siorTeam/smart-pen/week5/Nano_33ble/Python-Data-Sampling-App/main.py

# 파이썬 앱을 통해 데이터값들을 csv 파일로 만들어주는 코드입니다
# 이미 만들어진 파일에 덮어씌우기는 안되는 것 같습니다.
# pysimplegui 설치
# pyserial 설치
# 이 파일과 serial_comm 파일 같은 디렉토리에 넣기
# 만약 오류 뜨면 ktinker 설치

import csv
import queue
import re
import threading
from time import perf_counter

import PySimpleGUI as sg

import serial_comm as my_serial


class Application:

    def __init__(self, *args, **kwargs):
        super(Application, self).__init__(*args, **kwargs)
        baud_rate = 115200
        gui_queue = queue.Queue()
        serial_connector = my_serial.SerialObj(baud_rate)

        headerFont = ('Helvetica', 16)
        middleFont = ('Helvetica', 14)
        contextFont = ('Helvetica', 12)
        smallFont = ('Helvetica', 10)
        sg.theme('DarkBlue')

        layout = [[sg.Text('GET ACCELEROMETER GYROSCOPE\nSAMPLING DATA VIA SERIAL', font=headerFont)],
                  [sg.Text('Select your serial port', font=contextFont),
                   sg.Button('Serial Port Reload', size=(20, 1), font=smallFont)],
                  [sg.Listbox(values=[x[0] for x in my_serial.SerialObj.get_ports()],
                              size=(40, 6),
                              key='_SERIAL_PORT_LIST_',
                              font=contextFont,
                              enable_events=True)],
                  [sg.Text('', key='_SERIAL_PORT_CONFIRM_', size=(40, 1), font=middleFont, ), ],
                  [sg.Text('Buad Rate: {} bps'.format(baud_rate), size=(40, 1), font=middleFont, ), ],
                  [sg.Text('How many samples?', font=contextFont, ), sg.VerticalSeparator(),
                   sg.Input(do_not_clear=True, enable_events=True, key='_SAMPLE_IN_', font=contextFont, )],

                  [sg.HorizontalSeparator()],
                  [sg.Text('Serial Comm Status', font=contextFont, pad=((6, 0), (20, 0))), ],
                  [sg.Text('', key='_OUTPUT_', size=(40, 2), font=middleFont, ), ],
                  [sg.Button('Start', key='_ACT_BUTTON_', font=middleFont, size=(40, 1), pad=((0, 0), (0, 0)))],
                  [sg.Button('Exit', font=middleFont, size=(40, 1), pad=((0, 0), (20, 0)))],
                  [sg.Text('ThatProject - Version: 0.1', justification='right', size=(50, 1), font=smallFont, ), ]]

        self.window = sg.Window('Simple Serial Application', layout, size=(320, 440), keep_on_top=True)

        while True:
            event, values = self.window.Read(timeout=100)

            if event is None or event == 'Exit':
                break

            if event == 'Serial Port Reload':
                self.get_ports()

            if event == '_SERIAL_PORT_LIST_':
                self.window['_SERIAL_PORT_CONFIRM_'].update(value=self.window['_SERIAL_PORT_LIST_'].get()[0])

            if event == '_SAMPLE_IN_' and values['_SAMPLE_IN_'] and values['_SAMPLE_IN_'][-1] not in ('0123456789'):
                self.window['_SAMPLE_IN_'].update(values['_SAMPLE_IN_'][:-1])

            if event == '_ACT_BUTTON_':
                print(self.window[event].get_text())
                if self.window[event].get_text() == 'Start':

                    if len(self.window['_SERIAL_PORT_LIST_'].get()) == 0:
                        self.popup_dialog('Serial Port is not selected yet!', 'Serial Port', contextFont)

                    elif len(self.window['_SAMPLE_IN_'].get()) == 0:
                        self.popup_dialog('Set Sampling Count', 'Sampling Number Error', contextFont)

                    else:
                        self.stop_thread_trigger = False
                        self.thread_serial = threading.Thread(target=self.start_serial_comm,
                                                              args=(serial_connector,
                                                                    self.window[
                                                                        '_SERIAL_PORT_LIST_'].get()[
                                                                        0],
                                                                    int(self.window[
                                                                            '_SAMPLE_IN_'].get()),
                                                                    gui_queue, lambda: self.stop_thread_trigger),
                                                              daemon=True)
                        self.thread_serial.start()
                        self.window['_ACT_BUTTON_'].update('Stop')

                else:
                    self.stop_thread_trigger = True
                    self.thread_serial.join()
                    self.window['_ACT_BUTTON_'].update('Start')

            try:
                message = gui_queue.get_nowait()
            except queue.Empty:
                message = None
            if message is not None:
                self.window['_OUTPUT_'].Update(message)
                if 'Done' in message:
                    self.window['_ACT_BUTTON_'].update('Start')
                    self.popup_dialog(message, 'Success', contextFont)

        self.window.Close()

    def popup_dialog(self, contents, title, font):
        sg.Popup(contents, title=title, keep_on_top=True, font=font)

    def get_ports(self):
        self.window['_SERIAL_PORT_LIST_'].Update(values=[x[0] for x in my_serial.SerialObj.get_ports()])

    def start_serial_comm(self, serial_connector, serialport, sample_num, gui_queue, stop_thread_trigger):

        start_time = 0
        
        serial_connector.connect(serialport)
        if serial_connector.is_connect():

            gui_queue.put('Serial Connected!!')

            n = 0
            while n < sample_num:

                try:
                    if stop_thread_trigger():
                        break

                    data = serial_connector.get_data()
                    if data is not None:

                        if n == 0:
                            gui_queue.put(' - Data Transmitting ::: Wait! ')
                            start_time = perf_counter()

                        decode_string = data.decode('utf-8')
                        print(decode_string)
                        if len(decode_string.split(',')) == 9:
                            n += 1
                            percent = n / sample_num * 100
                            self.csv_writer('LoggedData_CalInertialAndMag.csv', n, decode_string)

                            if percent % 10 == 0:
                                gui_queue.put('Saving to CSV File: {}% complete'.format(int(percent)))

                except OSError as error:
                    print(error)

                except UnicodeDecodeError as error:
                    print(error)

        serial_connector.disconnect()
        time_taken = (perf_counter() - start_time)
        sampling_rate = sample_num / time_taken
        gui_queue.put('Sampling Rate: {} hz ::: Done!'.format(int(sampling_rate)))
        return

    def csv_writer(self, filename, index, data):
        with open(filename, 'a', newline='') as f:
            writer = csv.writer(f, delimiter=",", quoting=csv.QUOTE_NONE, escapechar=' ')
            writer.writerow([(index-1)*2, re.sub(r"\s+", "", data)])


if __name__ == '__main__':
    Application()
