siorTeam/smart-pen/week2/whdcks/mpu9250_transmitter/mpu9250_transmitter.ino

#include "Wire.h"

// I2Cdev and MPU9250 must be installed as libraries, or else the .cpp/.h files
// for both classes must be in the include path of your project
#include "I2Cdev.h"
#include "MPU9250.h"

// class default I2C address is 0x68
// specific I2C addresses may be passed as a parameter here
// AD0 low = 0x68 (default for InvenSense evaluation board)
// AD0 high = 0x69
#define sample_num_mdate  5000

MPU9250 accelgyro;
I2Cdev   I2C_M;

uint8_t buffer_m[6];

int16_t ax, ay, az;
int16_t gx, gy, gz;
int16_t   mx, my, mz;

float Axyz[3];
float Gxyz[3];
float Mxyz[3];


volatile float mx_sample[3];
volatile float my_sample[3];
volatile float mz_sample[3];

static float mx_centre = 0;
static float my_centre = 0;
static float mz_centre = 0;

volatile int mx_max = 0;
volatile int my_max = 0;
volatile int mz_max = 0;

volatile int mx_min = 0;
volatile int my_min = 0;
volatile int mz_min = 0;


void setup()
{
    // join I2C bus (I2Cdev library doesn't do this automatically)
    Wire.begin();

    // initialize serial communication
    // (38400 chosen because it works as well at 8MHz as it does at 16MHz, but
    // it's really up to you depending on your project)
    Serial.begin(115200);

    accelgyro.initialize();

    // verify connection
   //Serial.println("Testing device connections...");
    if(!accelgyro.testConnection())
    {
      Serial.println("MPU9250 connection failed");
    }
    



    delay(1000);
    
}



void loop()
{

    getAccel_Data();
    getGyro_Data();
    getCompassDate_calibrated(); 


    Serial.print(Gxyz[0], 10);
    Serial.print(", ");
    Serial.print(Gxyz[1], 10);
    Serial.print(", ");
    Serial.print(Gxyz[2], 10);
    Serial.print(", ");

    Serial.print(Axyz[0], 10);
    Serial.print(", ");
    Serial.print(Axyz[1], 10);
    Serial.print(", ");
    Serial.print(Axyz[2], 10);
    Serial.print(", ");
    Serial.print(Mxyz[0], 10);
    Serial.print(", ");
    Serial.print(Mxyz[1], 10);
    Serial.print(", ");
    Serial.print(Mxyz[2], 10);
    Serial.print("\n");

}


void Mxyz_init_calibrated ()
{

    Serial.println(F("Before using 9DOF,we need to calibrate the compass frist,It will takes about 2 minutes."));
    Serial.print("  ");
    Serial.println(F("During  calibratting ,you should rotate and turn the 9DOF all the time within 2 minutes."));
    Serial.print("  ");
    Serial.println(F("If you are ready ,please sent a command data 'ready' to start sample and calibrate."));
    while (!Serial.find("ready"));
    Serial.println("  ");
    Serial.println("ready");
    Serial.println("Sample starting......");
    Serial.println("waiting ......");

    get_calibration_Data ();

    Serial.println("     ");
    Serial.println("compass calibration parameter ");
    Serial.print(mx_centre);
    Serial.print("     ");
    Serial.print(my_centre);
    Serial.print("     ");
    Serial.println(mz_centre);
    Serial.println("    ");
}


void get_calibration_Data ()
{
    for (int i = 0; i < sample_num_mdate; i++)
    {
        get_one_sample_date_mxyz();
        /*
        Serial.print(mx_sample[2]);
        Serial.print(" ");
        Serial.print(my_sample[2]);                            //you can see the sample data here .
        Serial.print(" ");
        Serial.println(mz_sample[2]);
        */



        if (mx_sample[2] >= mx_sample[1])mx_sample[1] = mx_sample[2];
        if (my_sample[2] >= my_sample[1])my_sample[1] = my_sample[2]; //find max value
        if (mz_sample[2] >= mz_sample[1])mz_sample[1] = mz_sample[2];

        if (mx_sample[2] <= mx_sample[0])mx_sample[0] = mx_sample[2];
        if (my_sample[2] <= my_sample[0])my_sample[0] = my_sample[2]; //find min value
        if (mz_sample[2] <= mz_sample[0])mz_sample[0] = mz_sample[2];

    }

    mx_max = mx_sample[1];
    my_max = my_sample[1];
    mz_max = mz_sample[1];

    mx_min = mx_sample[0];
    my_min = my_sample[0];
    mz_min = mz_sample[0];



    mx_centre = (mx_max + mx_min) / 2;
    my_centre = (my_max + my_min) / 2;
    mz_centre = (mz_max + mz_min) / 2;

}

void get_one_sample_date_mxyz()
{
    getCompass_Data();
    mx_sample[2] = Mxyz[0];
    my_sample[2] = Mxyz[1];
    mz_sample[2] = Mxyz[2];
}


void getAccel_Data(void)
{
    accelgyro.getMotion9(&ax, &ay, &az, &gx, &gy, &gz, &mx, &my, &mz);
    Axyz[0] = (double) ax / 16384;
    Axyz[1] = (double) ay / 16384;
    Axyz[2] = (double) az / 16384;
}


void getGyro_Data(void)
{
    accelgyro.getMotion9(&ax, &ay, &az, &gx, &gy, &gz, &mx, &my, &mz);

    Gxyz[0] = (double) gx * 250 / 32768;
    Gxyz[1] = (double) gy * 250 / 32768;
    Gxyz[2] = (double) gz * 250 / 32768;
}

void getCompass_Data(void)
{
    I2C_M.writeByte(MPU9150_RA_MAG_ADDRESS, 0x0A, 0x01); //enable the magnetometer
    delay(10);
    I2C_M.readBytes(MPU9150_RA_MAG_ADDRESS, MPU9150_RA_MAG_XOUT_L, 6, buffer_m);




    mx = ((int16_t)(buffer_m[1]) << 8) | buffer_m[0] ;
    my = ((int16_t)(buffer_m[3]) << 8) | buffer_m[2] ;
    mz = ((int16_t)(buffer_m[5]) << 8) | buffer_m[4] ;


    Mxyz[0] = (double) mx * 1200 / 4096;
    Mxyz[1] = (double) my * 1200 / 4096;
    Mxyz[2] = (double) mz * 1200 / 4096;
}

void getCompassDate_calibrated ()
{
    getCompass_Data();
    Mxyz[0] = Mxyz[0] - mx_centre;
    Mxyz[1] = Mxyz[1] - my_centre;
    Mxyz[2] = Mxyz[2] - mz_centre;
}
