siorTeam/smart-pen/week2/whdcks/Python-Data-Sampling-App/ESP32_GY-BNO055/ESP32_GY-BNO055.ino

#include <Wire.h>
#include <Adafruit_Sensor.h>
#include <Adafruit_BNO055.h>
#include <TFT_eSPI.h>
#define I2C_SDA 21
#define I2C_SCL 22

TwoWire I2CBNO = TwoWire(0);
Adafruit_BNO055 bno = Adafruit_BNO055(55, 0x29, &I2CBNO);
TFT_eSPI tft = TFT_eSPI();

void setup(){
  Serial.begin(115200);
  displayInit();

  I2CBNO.begin(I2C_SDA, I2C_SCL);

  if (!bno.begin()){
    printString("No BNO055 detected", TFT_BLACK, TFT_YELLOW);
    while (1){
      delay(10);
    }
  }

  delay(100);   

  uint8_t system, gyro, accel, mag = 0;
  while(system != 3) {
    bno.getCalibration(&system, &gyro, &accel, &mag);
    printString("Calibration!!!", TFT_WHITE, TFT_RED);
    delay(100); 
    }

  printString("READING...", TFT_BLACK, TFT_DARKGREEN);
  delay(100);
}

void loop(){

  delay(8); // To make sampling rate around 100hz

  imu::Vector<3> acc = bno.getVector(Adafruit_BNO055::VECTOR_ACCELEROMETER); 
  imu::Vector<3> gyr = bno.getVector(Adafruit_BNO055::VECTOR_GYROSCOPE);  

  Serial.print(gyr.x(),4); 
  Serial.print(", "); 
  Serial.print(gyr.y(),4);
  Serial.print(", "); 
  Serial.print(gyr.z(),4);
  Serial.print(", "); 
  Serial.print(acc.x(), 4); 
  Serial.print(", "); 
  Serial.print(acc.y(),4); 
  Serial.print(", "); 
  Serial.println(acc.z(),4);
}

void displayInit(){
  tft.begin();
  tft.setRotation(1);
  tft.setTextColor(TFT_WHITE,TFT_BLACK); 
  tft.fillScreen(TFT_BLACK);
  tft.setSwapBytes(true);
  tft.setTextFont(4);
  tft.setTextDatum(MC_DATUM);
}

void printString(String text, uint16_t textColor, uint16_t bgColor){
  tft.fillScreen(bgColor);
  tft.setTextColor(textColor, bgColor);
  tft.drawCentreString(text, tft.width()/2, tft.height()/2, 4);
}
