siorTeam/smart-pen/week2/whdcks/Python-Data-Sampling-App/serial_comm.py

import serial
import serial.tools.list_ports


class SerialObj:

    def __init__(self, serial_speed):
        self.serial = None
        self.baud_rate = serial_speed

    @staticmethod
    def get_ports():
        return list(serial.tools.list_ports.comports())

    def connect(self, port):
        self.serial = serial.Serial(port, self.baud_rate)
        self.serial.flushInput()

    def is_connect(self):
        return self.serial.isOpen()

    def get_data(self):
        if not self.serial.isOpen():
            return None
        else:
            return self.serial.readline()

    def disconnect(self):
        if self.serial is None:
            return

        self.serial.close()
